mp619/Aqua-Polis/SensorModules/TDS_Test.py

import time
import TDS
import Turbidity as Turb

#State address of ADC
ADC_adr = 0x48

bus = TDS.init()


while True:
    total_TDS = 0
    total_Turb = 0
    TDS.config(bus, ADC_adr)
    time.sleep(1)
    for i in range(0,10):
        t1 = TDS.read(bus, ADC_adr)
        total_TDS = total_TDS + t1
    avg_TDS = total_TDS/10
    Turb.config(bus, ADC_adr)
    time.sleep(1)
    for i in range(0,10):
        t2 = Turb.read(bus, ADC_adr)
        total_Turb = total_Turb + t2
    avg_Turb = total_Turb/10
    tds = TDS.convert(avg_TDS)
    turb = Turb.convert(avg_Turb)
    print(tds, 'ppm', turb, 'NTU') 
